nickbild/deepclean/camera_calibration/img/good/pi1_1_good.jpg

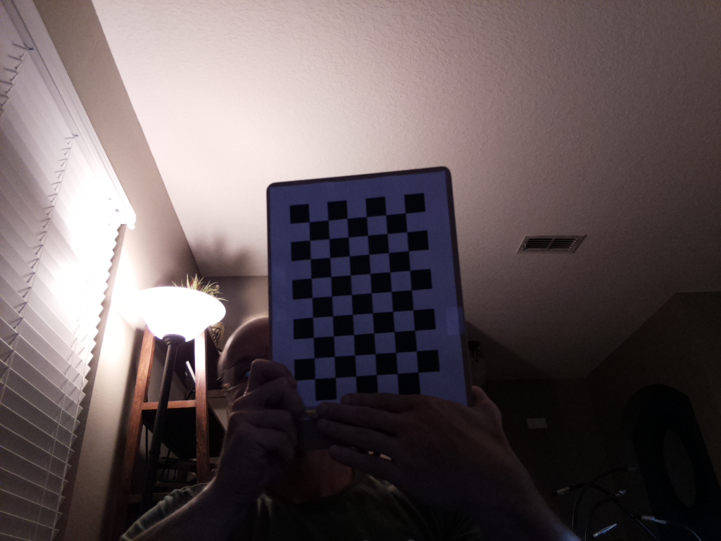
camera_calibration/img/good/pi1_1_good.jpg
