nickbild/deepclean/camera_calibration/img/good/pi1_5_good.jpg

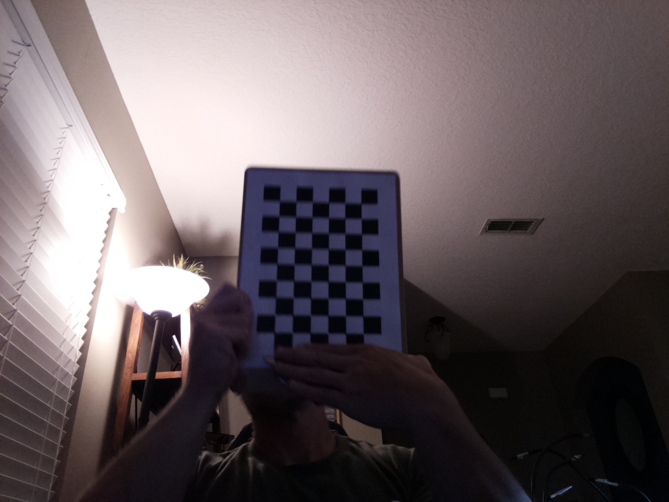
camera_calibration/img/good/pi1_5_good.jpg
