nickbild/deepclean/camera_calibration/img/good/pi1_6_good.jpg

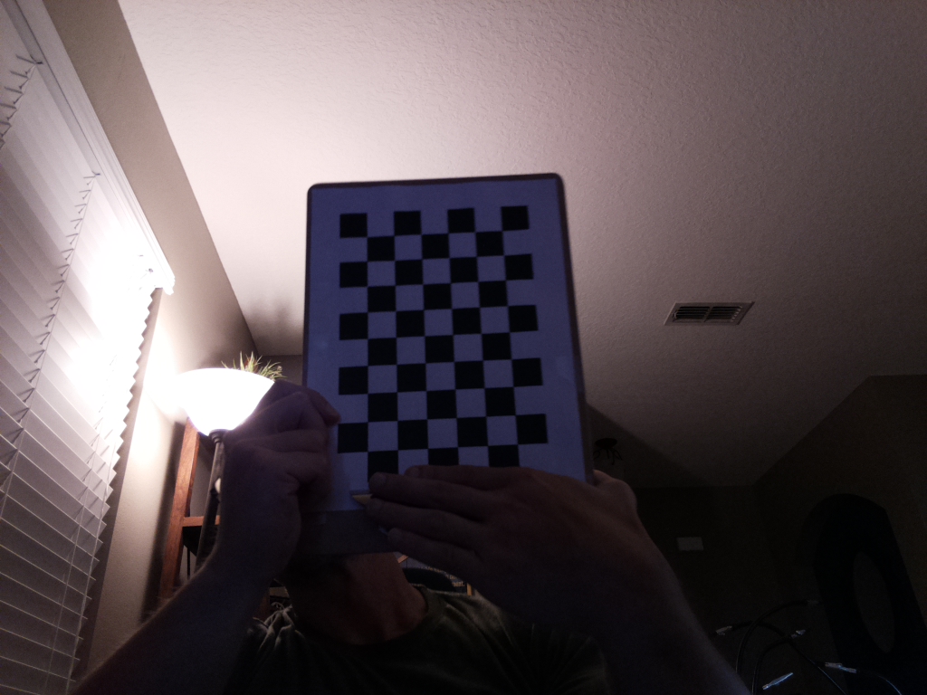
camera_calibration/img/good/pi1_6_good.jpg
