nickbild/deepclean/camera_calibration/img/good/pi1_7_good2.jpg

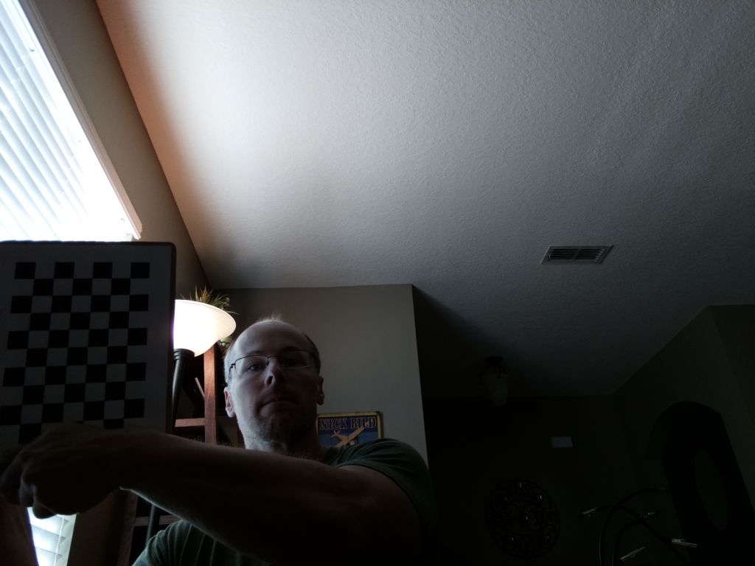
camera_calibration/img/good/pi1_7_good2.jpg
