nickbild/deepclean/camera_calibration/img/good/pi1_7_good.jpg

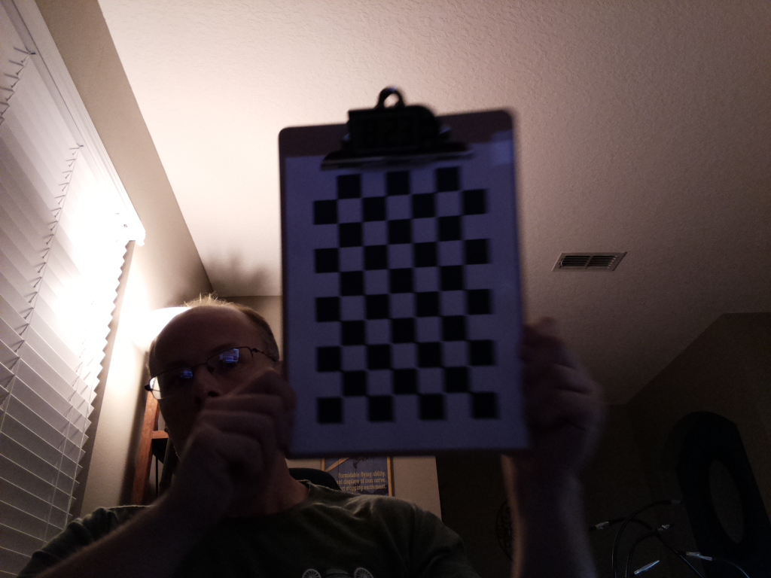
camera_calibration/img/good/pi1_7_good.jpg
