nickbild/deepclean/camera_calibration/img/good/pi1_9_good.jpg

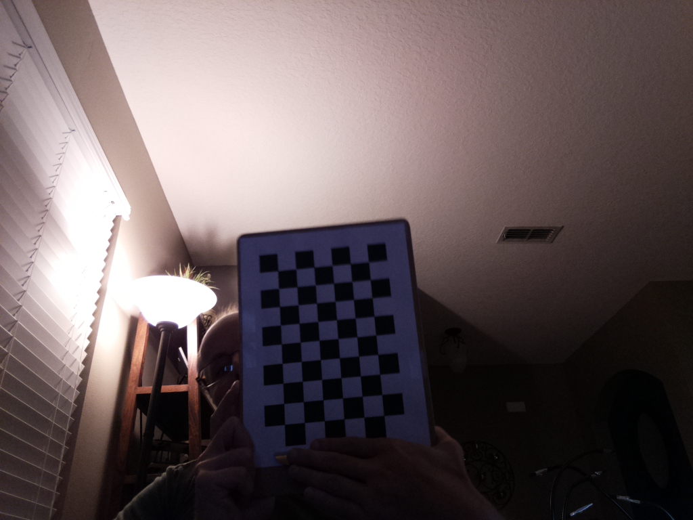
camera_calibration/img/good/pi1_9_good.jpg
