nickbild/deepclean/camera_calibration/img/good/pi1_11_good.jpg

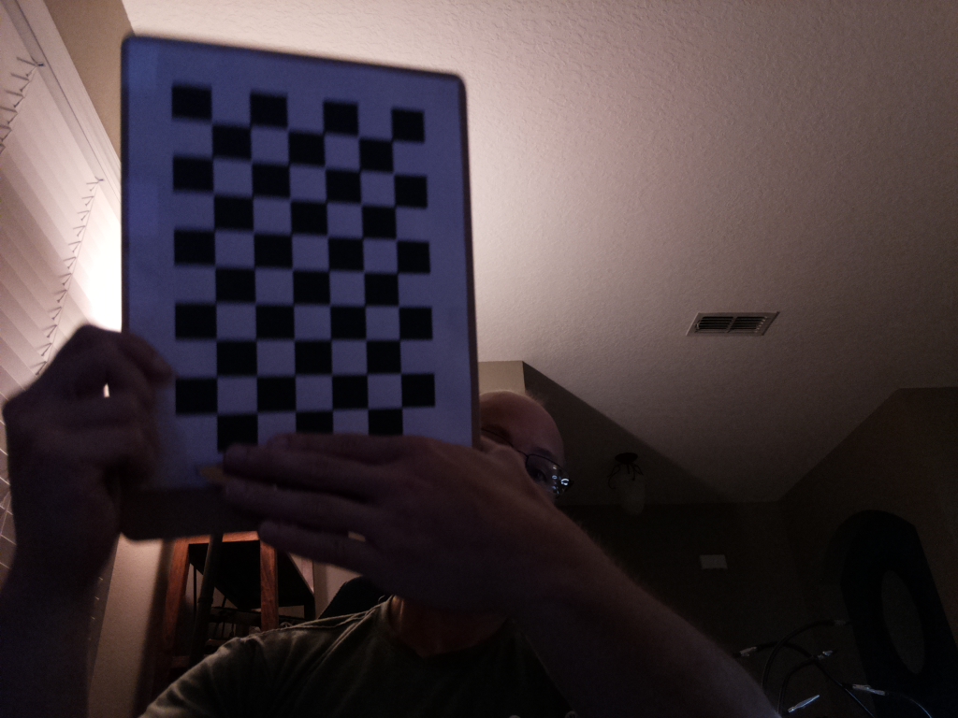
camera_calibration/img/good/pi1_11_good.jpg
