nickbild/deepclean/camera_calibration/img/good/pi1_12_good.jpg

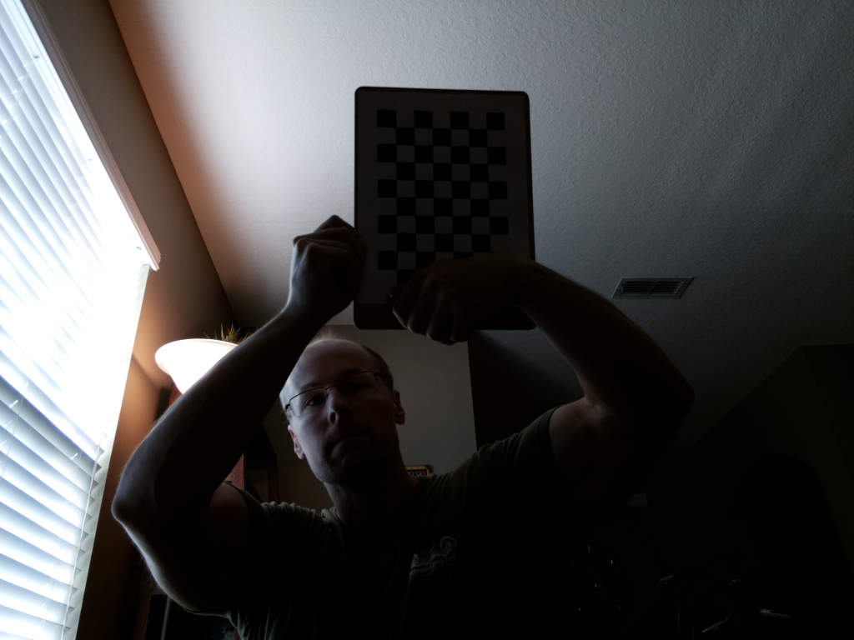
camera_calibration/img/good/pi1_12_good.jpg
