nickbild/deepclean/camera_calibration/img/good/pi1_15_good.jpg

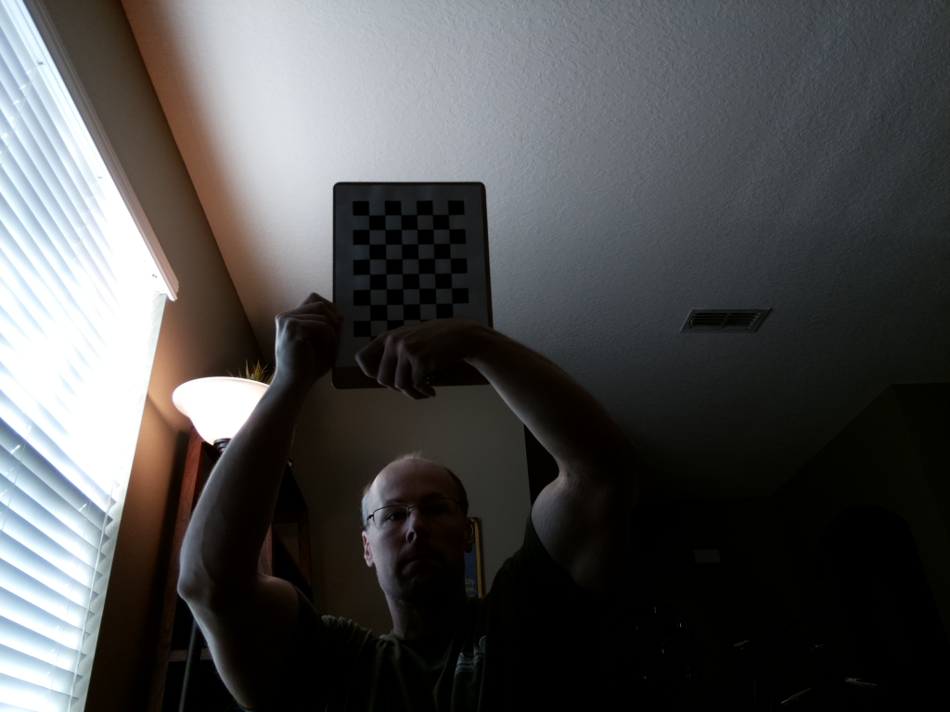
camera_calibration/img/good/pi1_15_good.jpg
