nickbild/deepclean/camera_calibration/img/good/pi1_16_good.jpg

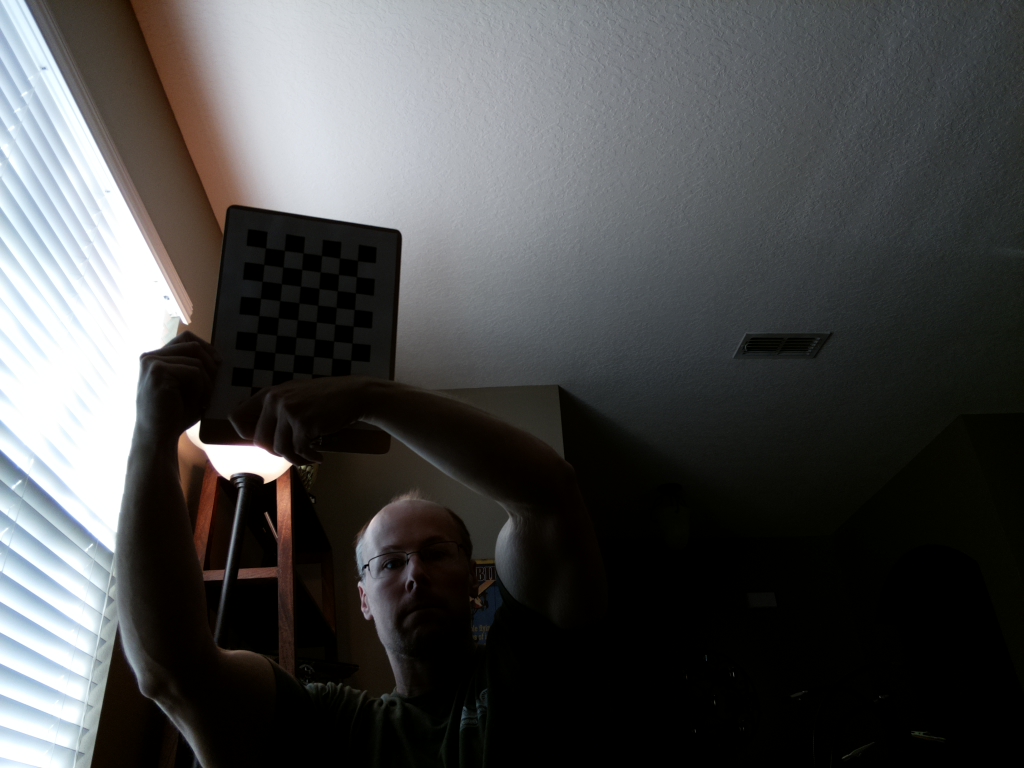
camera_calibration/img/good/pi1_16_good.jpg
