nickbild/deepclean/camera_calibration/img/good/pi1_17_good.jpg

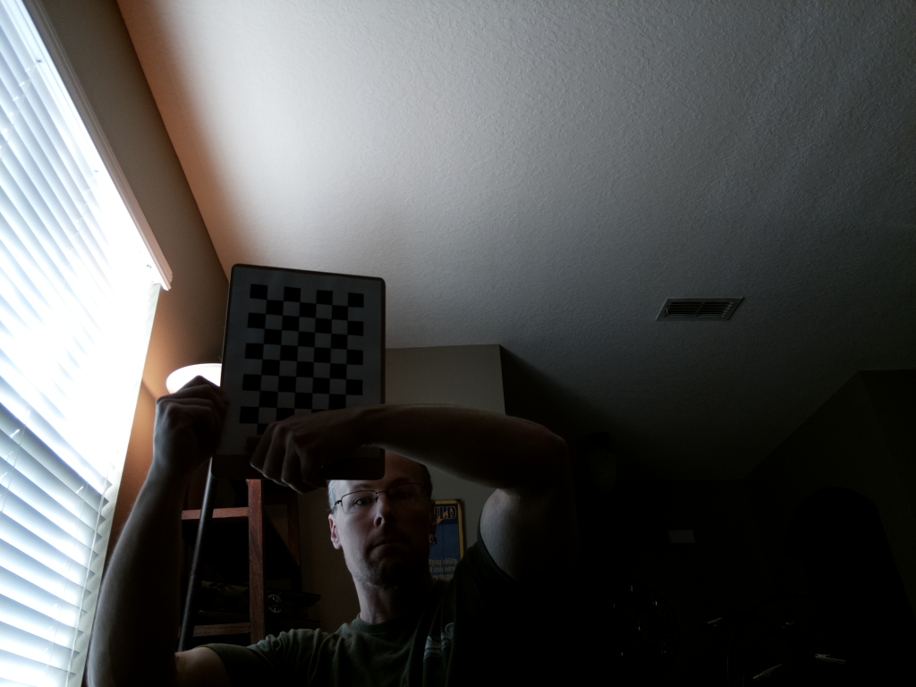
camera_calibration/img/good/pi1_17_good.jpg
