nickbild/deepclean/camera_calibration/img/good/pi1_30_good.jpg

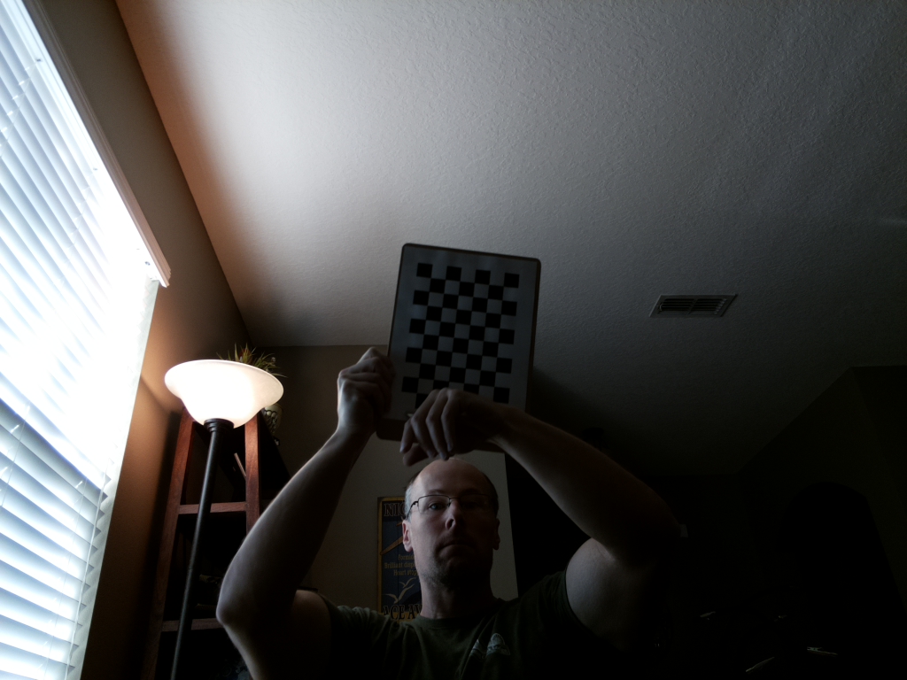
camera_calibration/img/good/pi1_30_good.jpg
