nickbild/deepclean/camera_calibration/img/good/pi1_31_good2.jpg

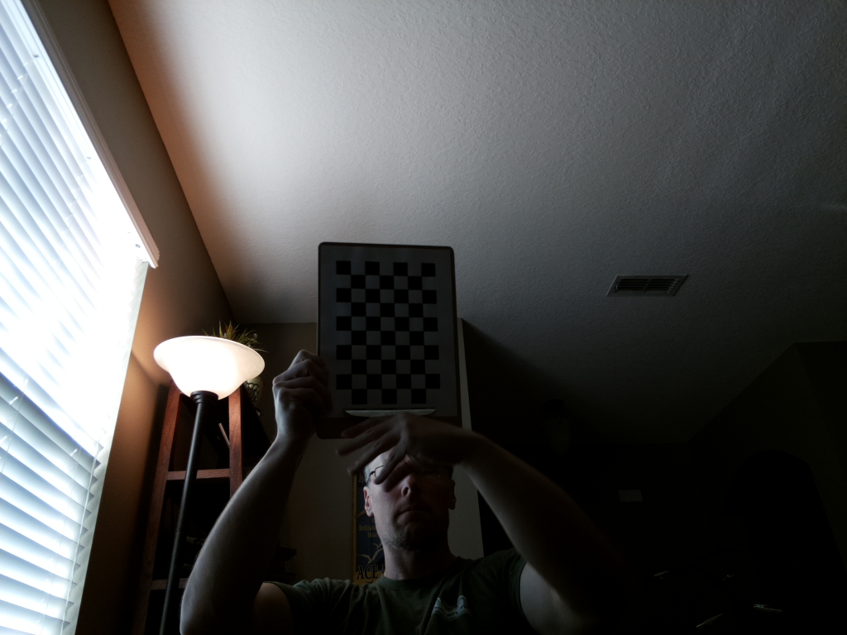
camera_calibration/img/good/pi1_31_good2.jpg
