nickbild/deepclean/camera_calibration/img/good/pi1_31_good.jpg

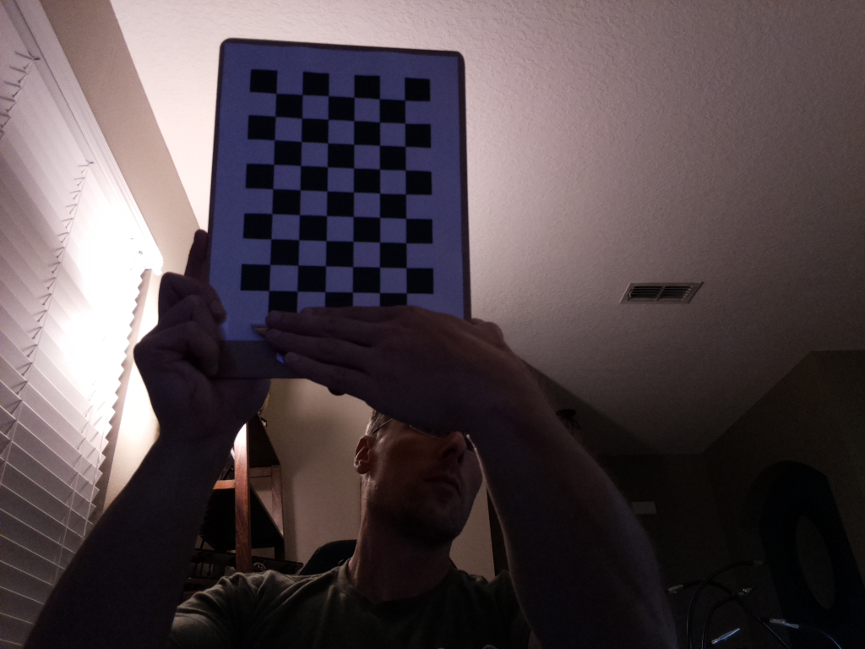
camera_calibration/img/good/pi1_31_good.jpg
