nickbild/deepclean/camera_calibration/img/good/pi1_32_good2.jpg

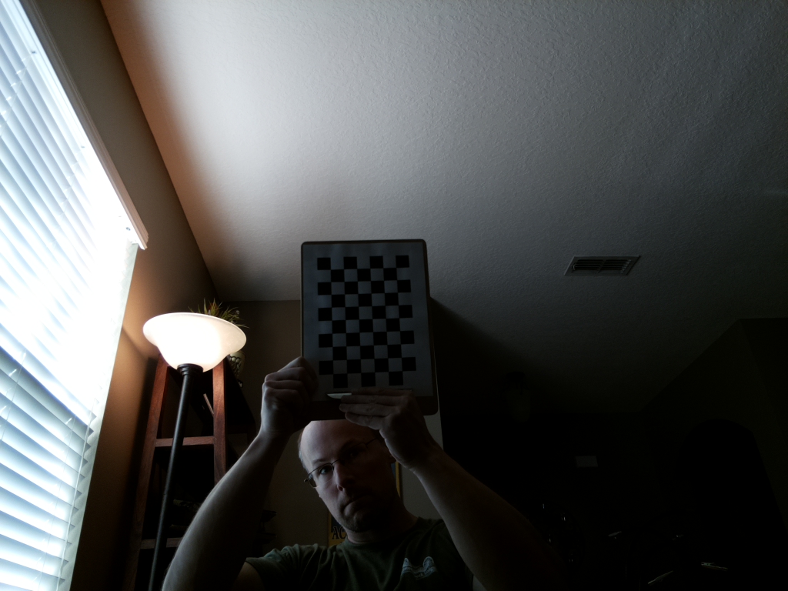
camera_calibration/img/good/pi1_32_good2.jpg
