nickbild/deepclean/camera_calibration/img/good/pi1_32_good.jpg

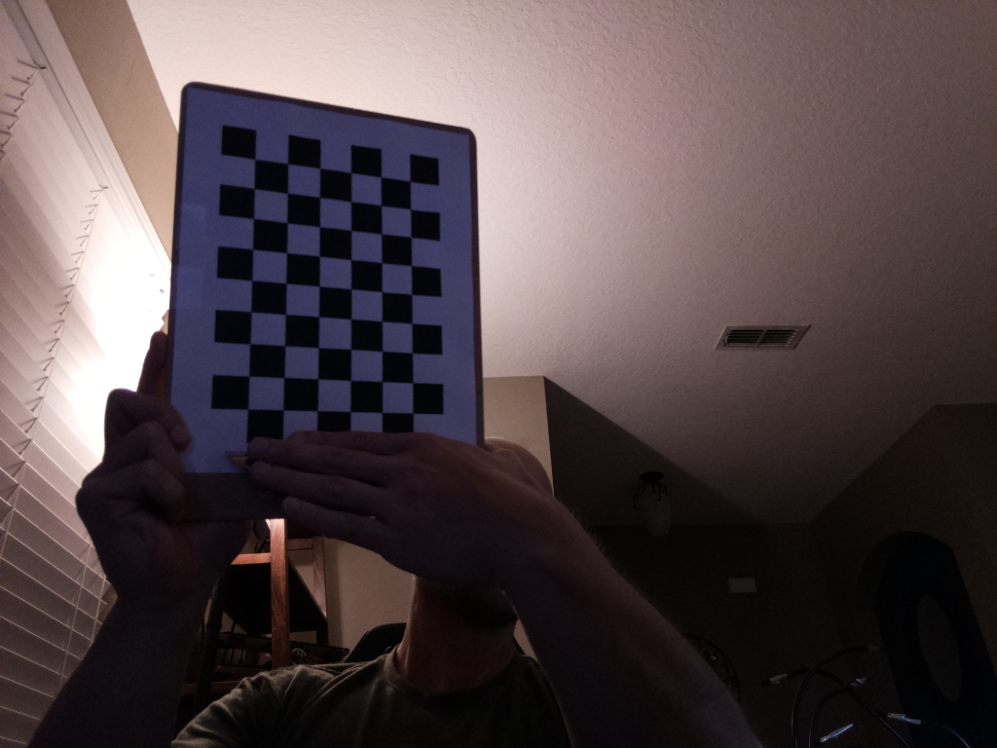
camera_calibration/img/good/pi1_32_good.jpg
