nickbild/deepclean/camera_calibration/img/good/pi1_33_good.jpg

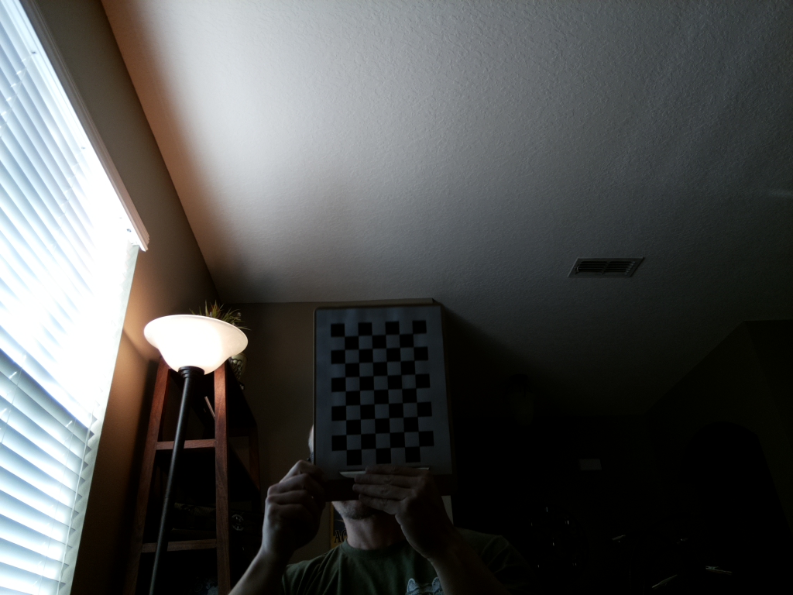
camera_calibration/img/good/pi1_33_good.jpg
