nickbild/deepclean/camera_calibration/img/good/pi1_55_good.jpg

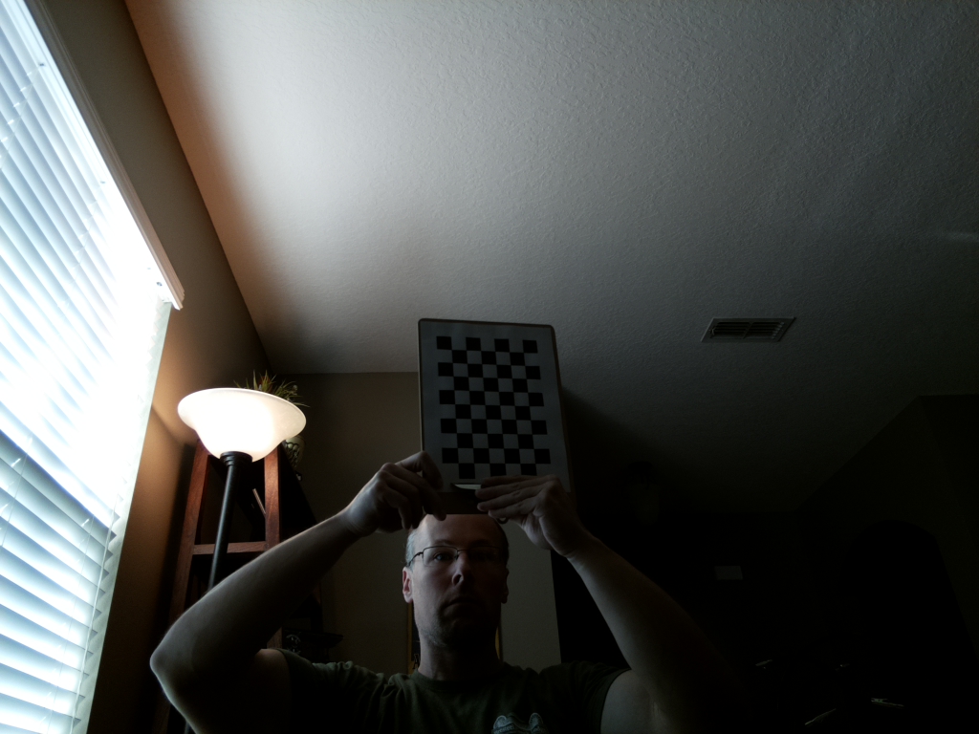
camera_calibration/img/good/pi1_55_good.jpg
