nickbild/deepclean/camera_calibration/img/good/pi2_3_good.jpg

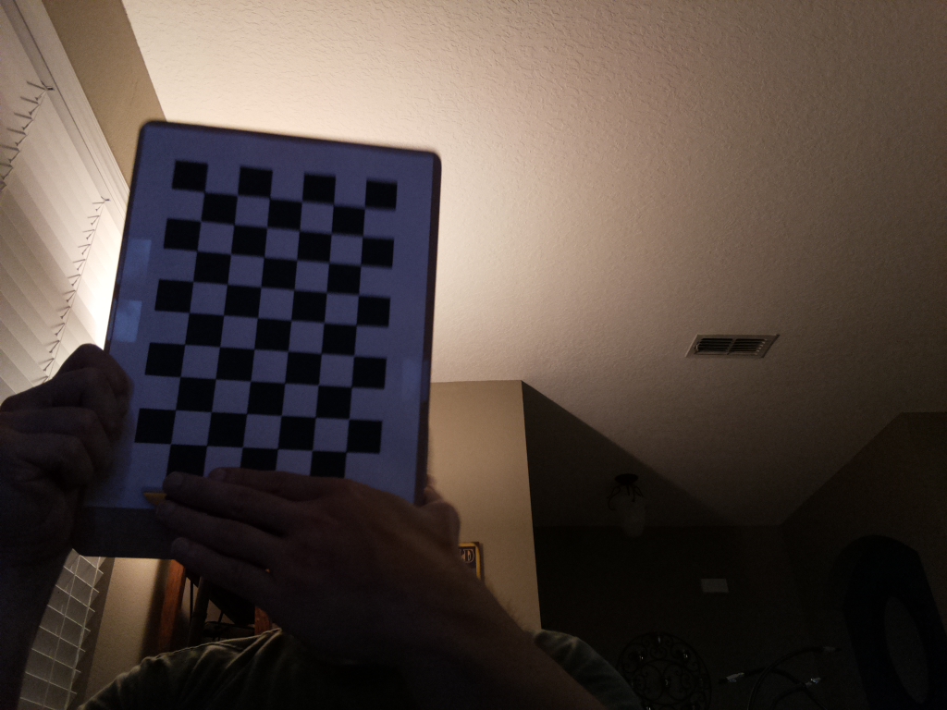
camera_calibration/img/good/pi2_3_good.jpg
