nickbild/deepclean/camera_calibration/img/good/pi2_5_good.jpg

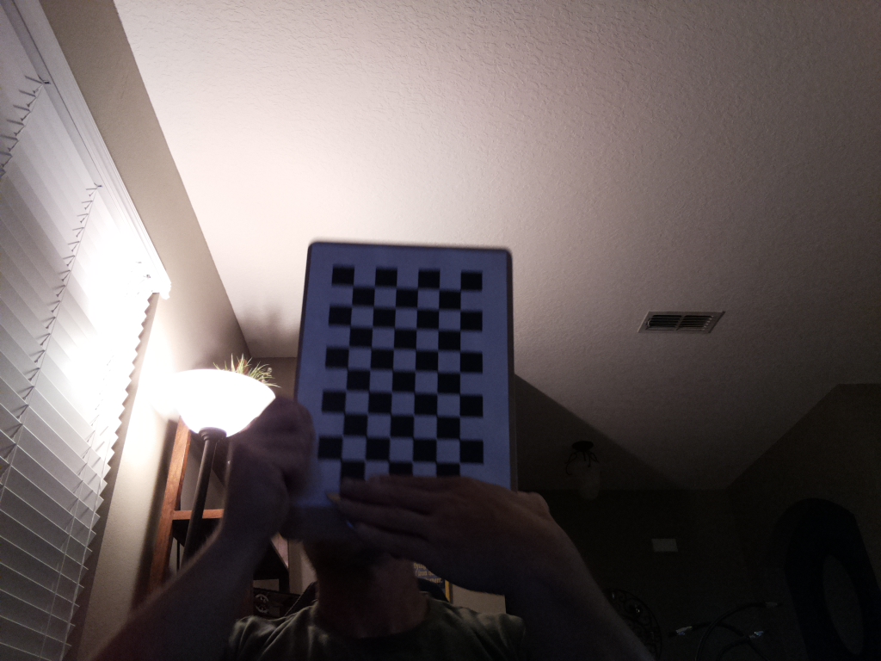
camera_calibration/img/good/pi2_5_good.jpg
