nickbild/deepclean/camera_calibration/img/good/pi2_6_good2.jpg

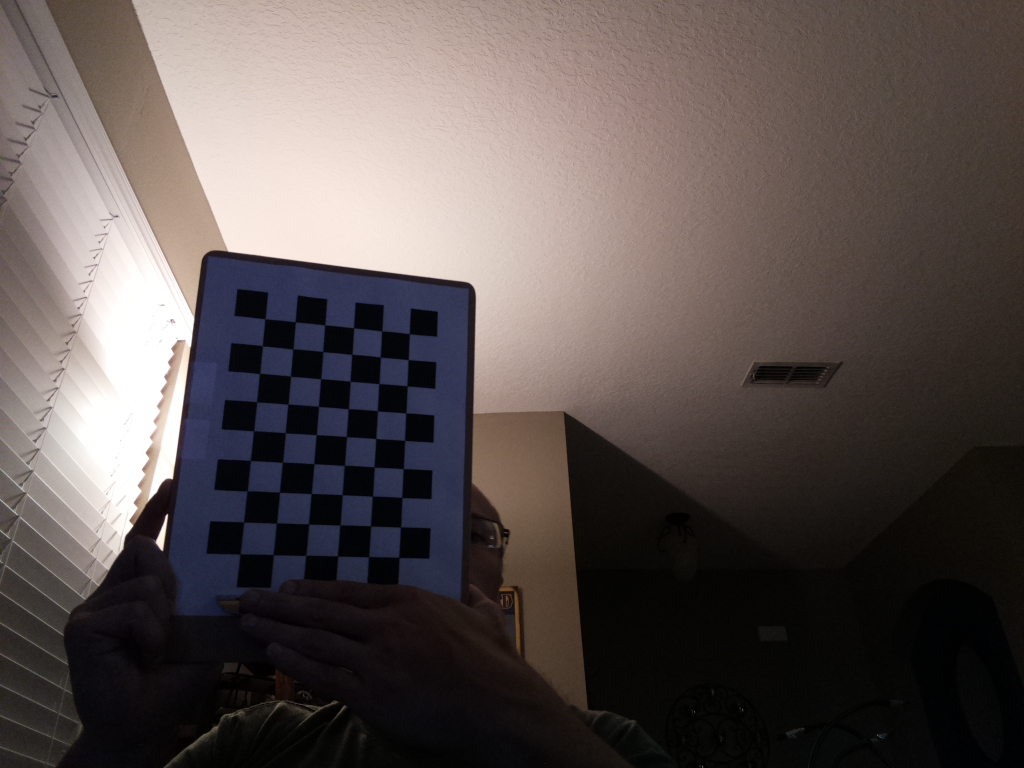
camera_calibration/img/good/pi2_6_good2.jpg
