nickbild/deepclean/camera_calibration/img/good/pi2_6_good.jpg

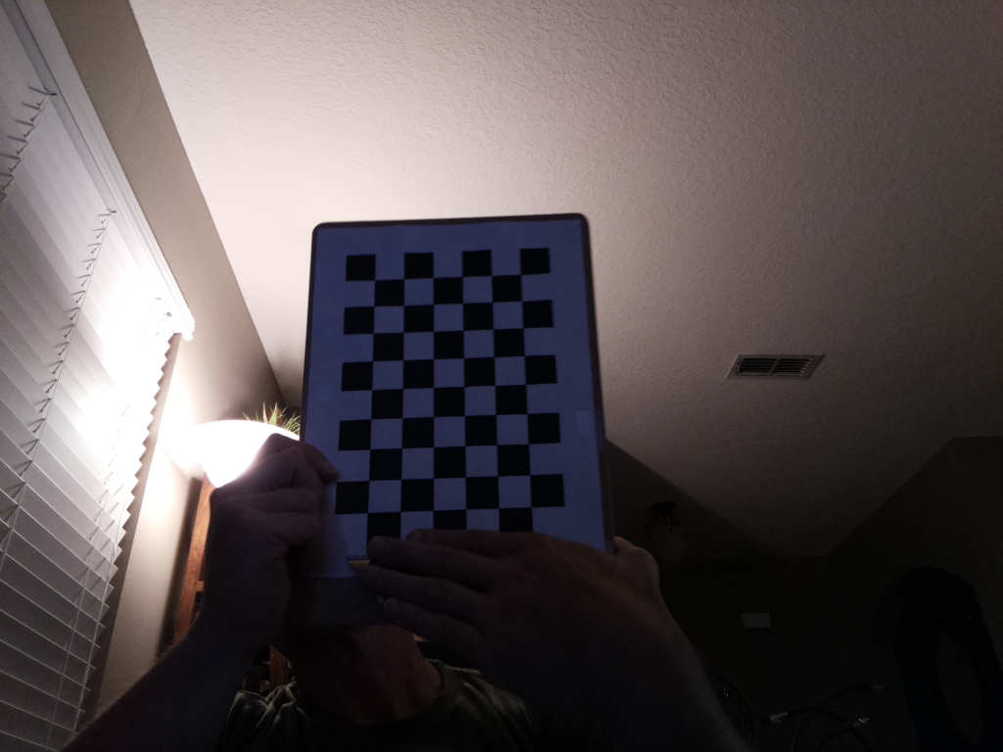
camera_calibration/img/good/pi2_6_good.jpg
