nickbild/deepclean/camera_calibration/img/good/pi2_7_good.jpg

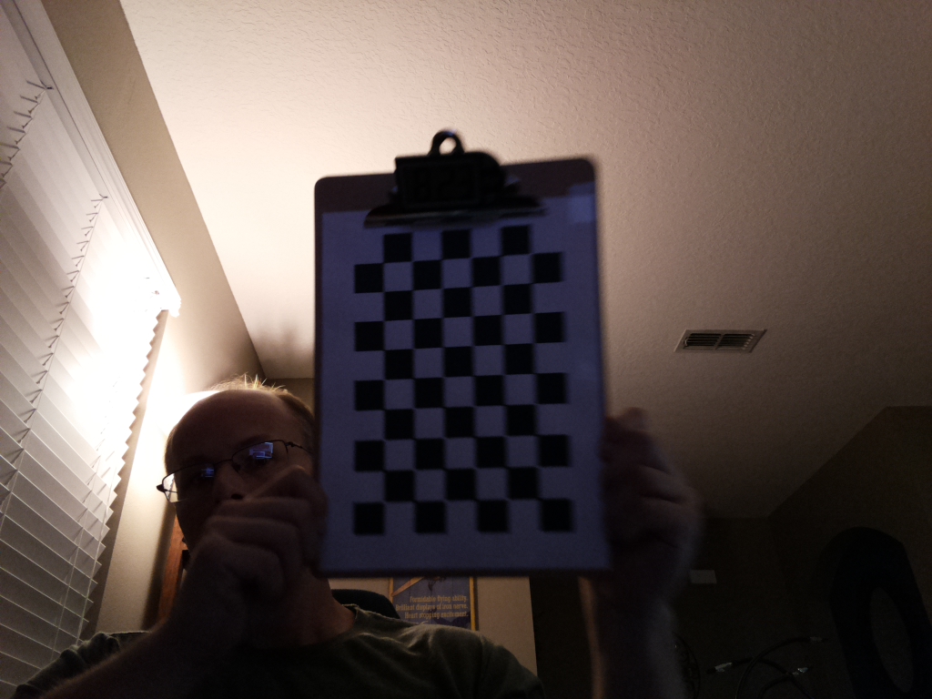
camera_calibration/img/good/pi2_7_good.jpg
