nickbild/deepclean/camera_calibration/img/good/pi2_11_good.jpg

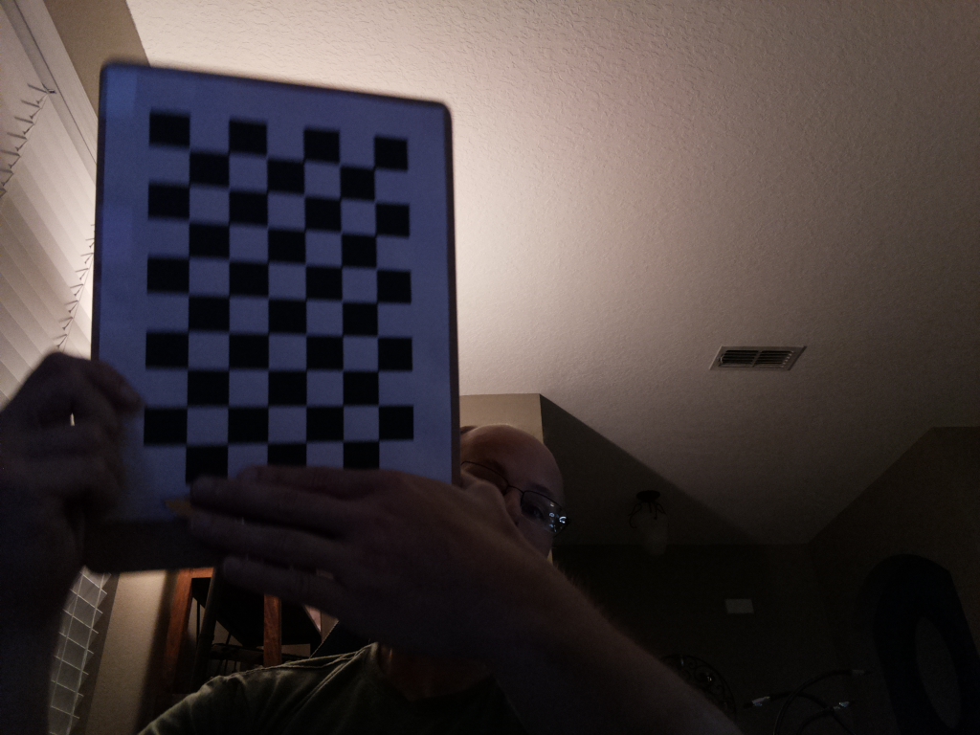
camera_calibration/img/good/pi2_11_good.jpg
