nickbild/deepclean/camera_calibration/img/good/pi2_12_good.jpg

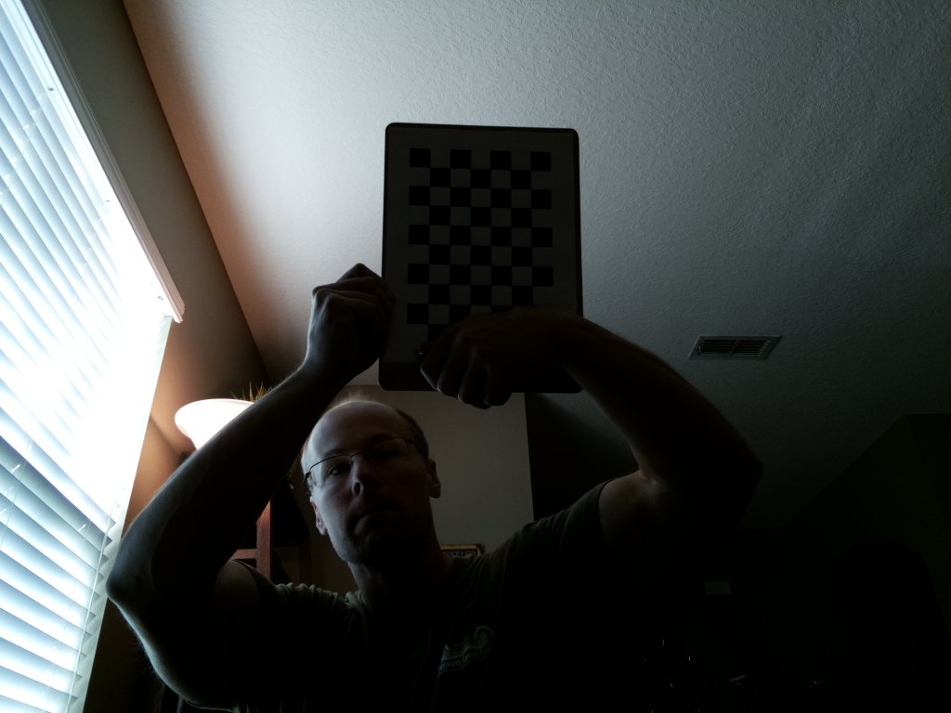
camera_calibration/img/good/pi2_12_good.jpg
