nickbild/deepclean/camera_calibration/img/good/pi2_15_good.jpg

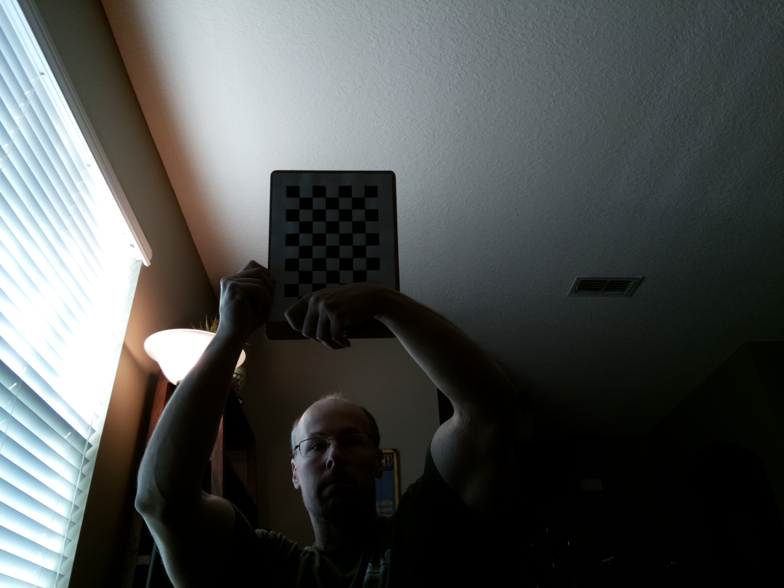
camera_calibration/img/good/pi2_15_good.jpg
