nickbild/deepclean/camera_calibration/img/good/pi2_16_good.jpg

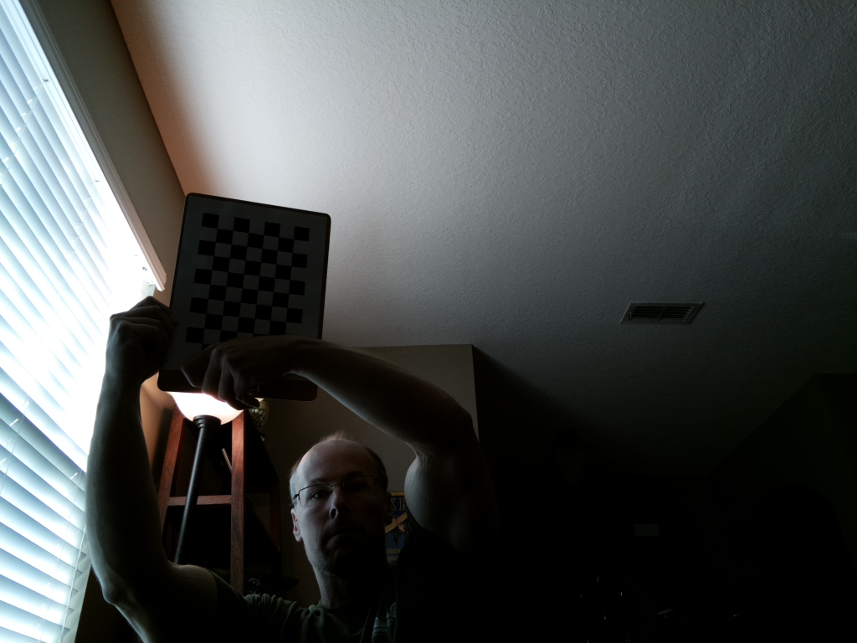
camera_calibration/img/good/pi2_16_good.jpg
