nickbild/deepclean/camera_calibration/img/good/pi2_17_good.jpg

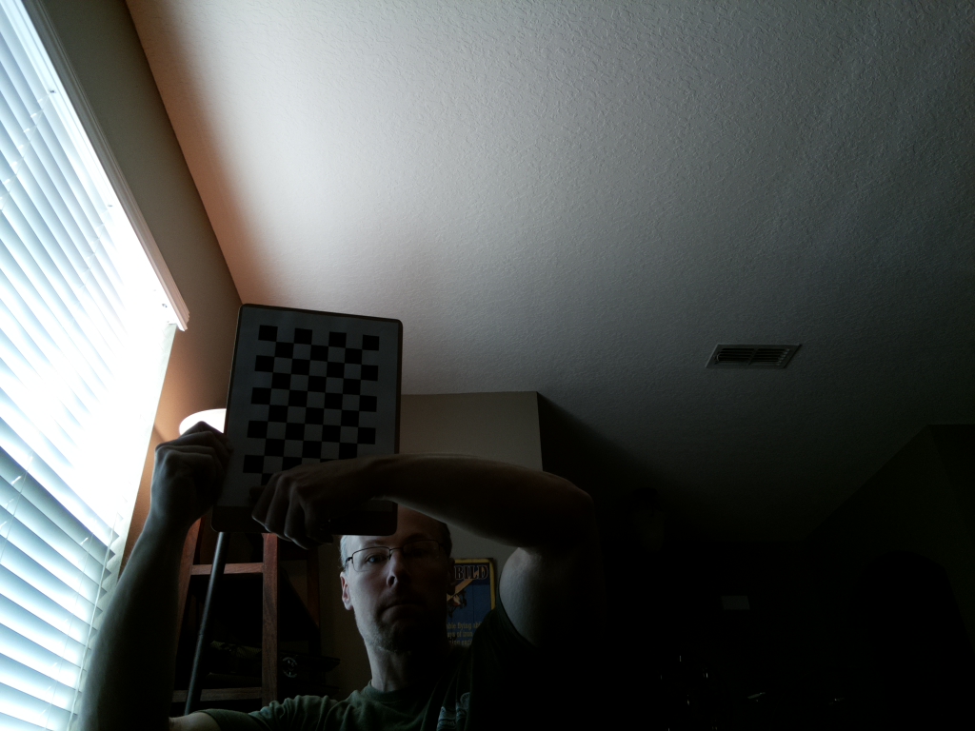
camera_calibration/img/good/pi2_17_good.jpg
