nickbild/deepclean/camera_calibration/img/good/pi2_19_good.jpg

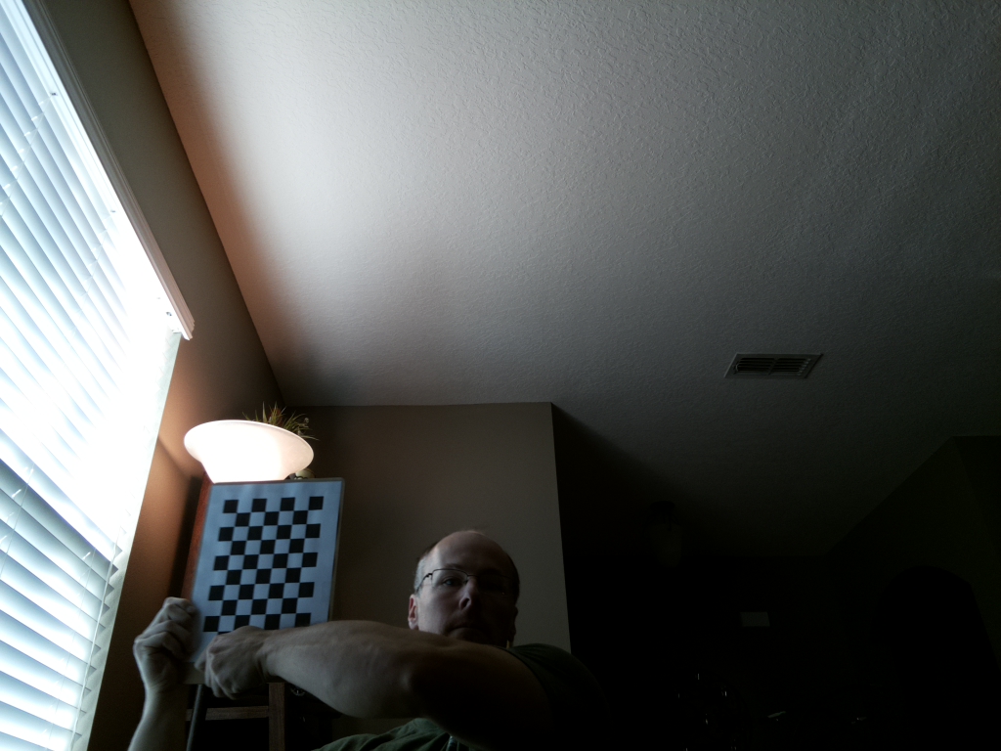
camera_calibration/img/good/pi2_19_good.jpg
