nickbild/deepclean/camera_calibration/img/good/pi2_30_good.jpg

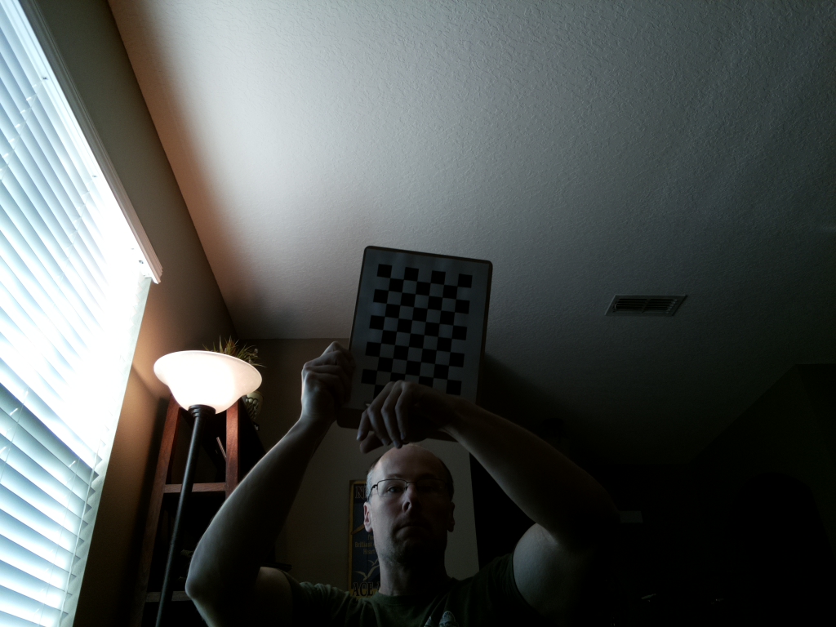
camera_calibration/img/good/pi2_30_good.jpg
