nickbild/deepclean/camera_calibration/img/good/pi2_32_good.jpg

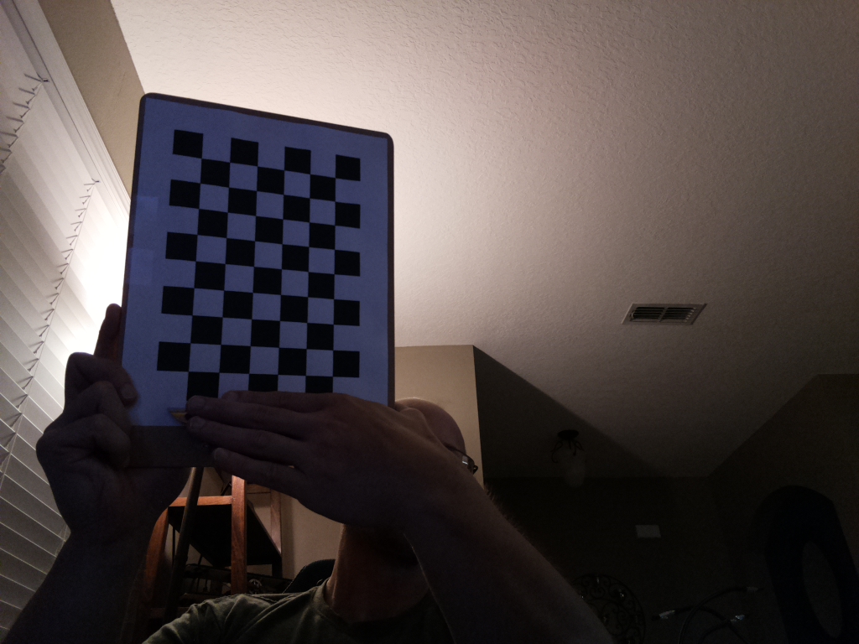
camera_calibration/img/good/pi2_32_good.jpg
