nickbild/deepclean/camera_calibration/img/good/pi2_33_good.jpg

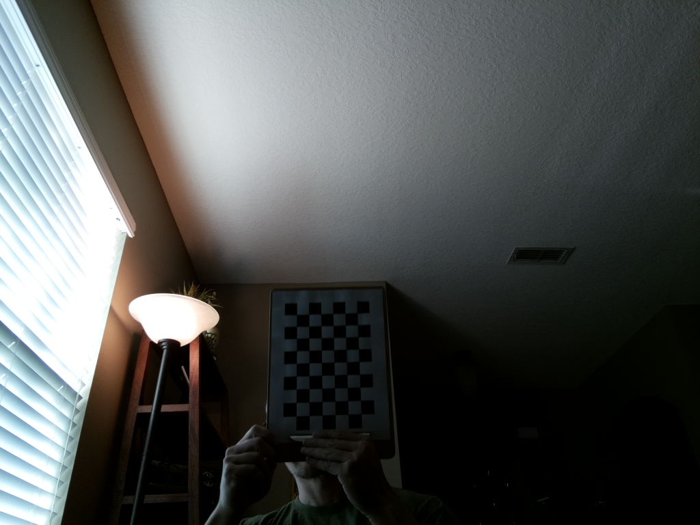
camera_calibration/img/good/pi2_33_good.jpg
