nickbild/deepclean/camera_calibration/img/good/pi2_34_good.jpg

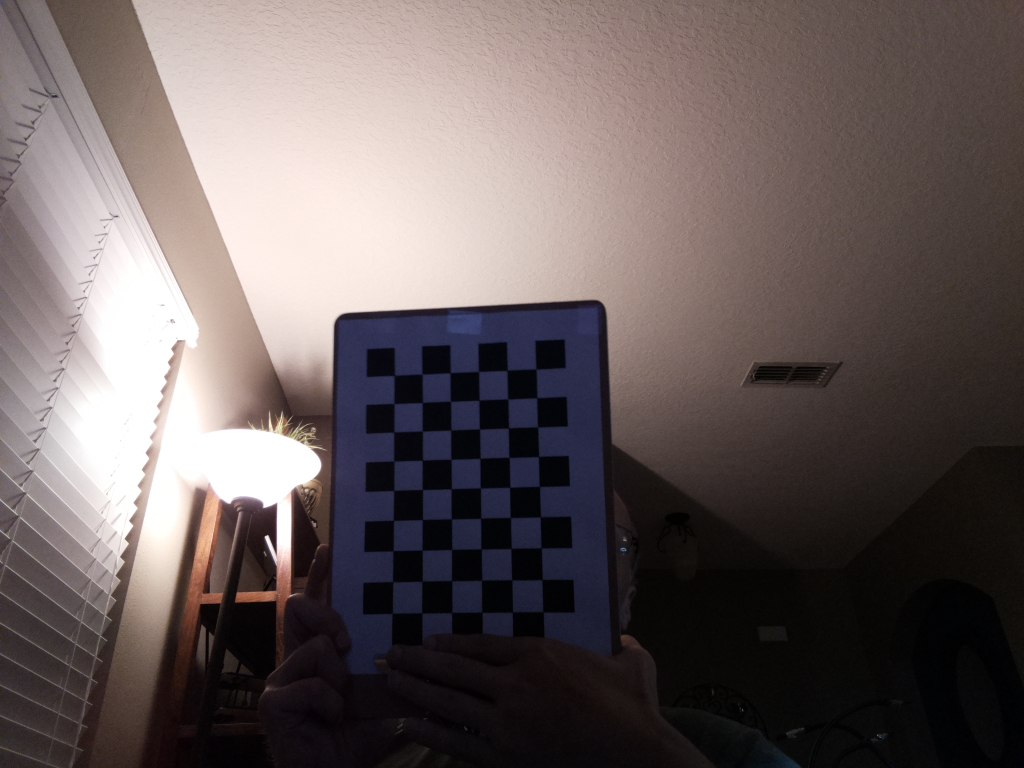
camera_calibration/img/good/pi2_34_good.jpg
