nickbild/deepclean/camera_calibration/img/good/pi2_55_good.jpg

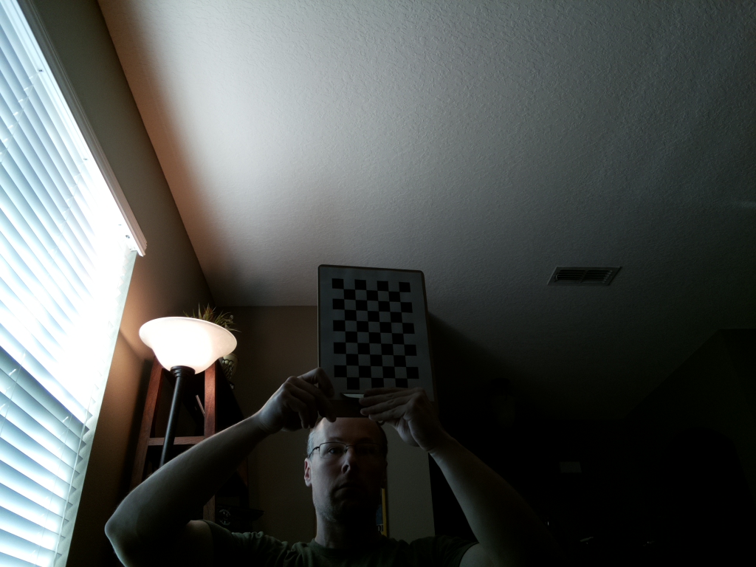
camera_calibration/img/good/pi2_55_good.jpg
