nickbild/deepclean/camera_calibration/img/good/pi2_59_good.jpg

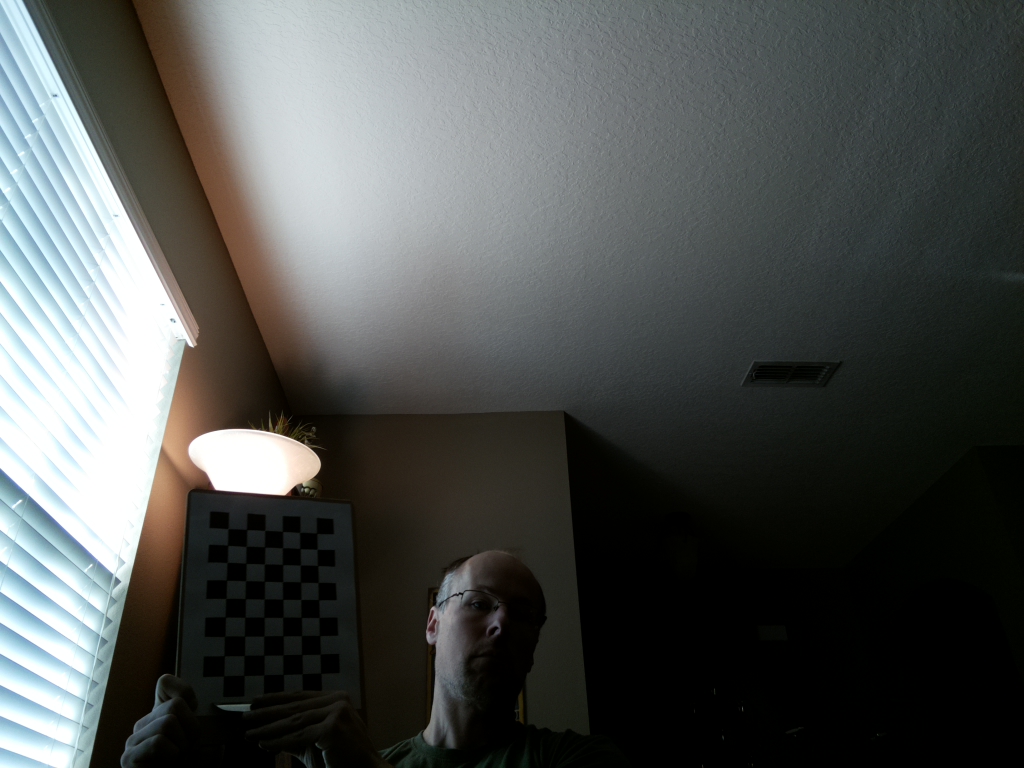
camera_calibration/img/good/pi2_59_good.jpg
